marrrk/LoRaDongle/docs/assets/images/LoRaDongle_V1.jpg

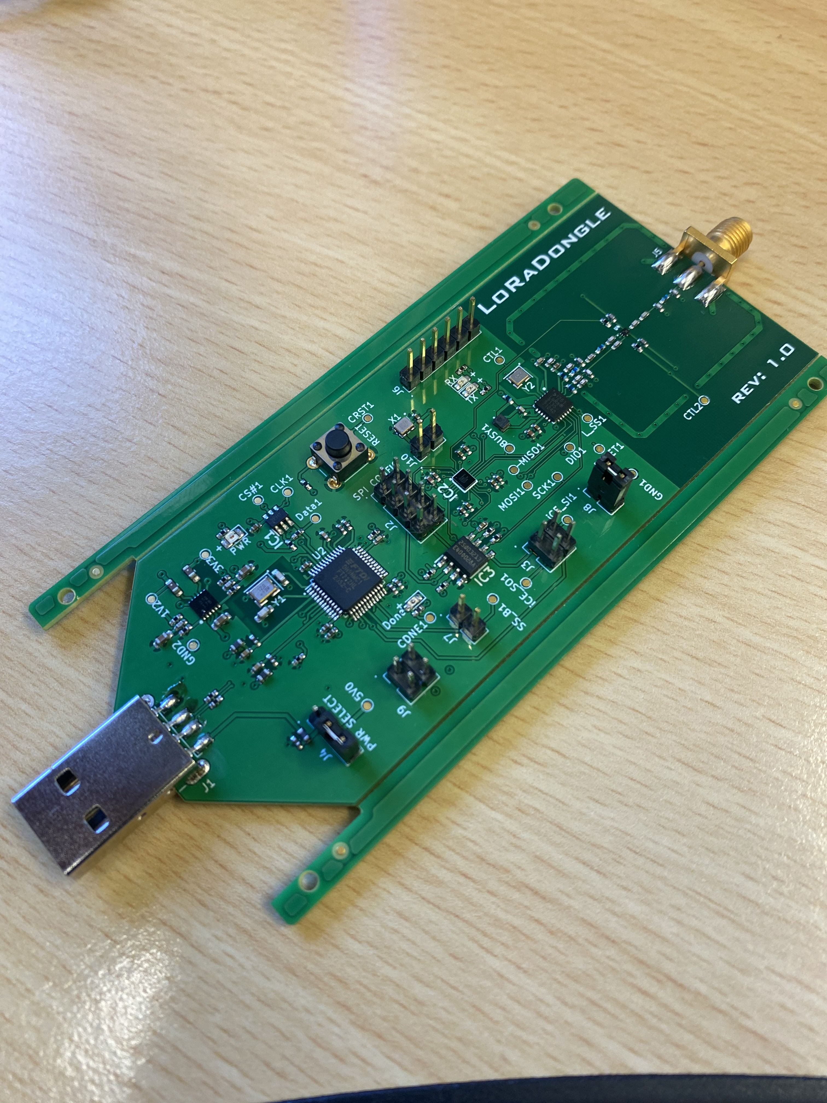
docs/assets/images/LoRaDongle_V1.jpg
