marrrk/LoRaDongle/testing/latency_tests/Test_11.csv

Success | Time to Send | Time to Receive | Message Size | RSSI | RSSI Despread | SNR | Timestamp
False | 9251.708523809524 |  |  |  |  |  | 17:50:10
False | 9251.708523809524 | 18680.361904761907 | 15 | -1.0 | -0.5 | 1.25 | 17:50:22
False | 9251.708523809524 |  |  |  |  |  | 17:50:58
False | 9251.708523809524 | 18680.49219047619 | 15 | -0.5 | -0.5 | 1.25 | 17:51:09
False | 9251.708523809524 |  |  |  |  |  | 17:51:46
False | 9251.708523809524 | 18680.49219047619 | 15 | -0.5 | -1.0 | 1.0 | 17:51:57
False | 9251.708523809524 |  |  |  |  |  | 17:52:34
False | 9251.708523809524 | 18680.49219047619 | 15 | -0.5 | -0.5 | 1.5 | 17:52:45
False | 9251.708523809524 | 18690.915047619048 | 15 | -0.5 | -0.5 | 1.25 | 17:53:09
False | 9251.708523809524 | 18691.17561904762 | 15 | -0.5 | -0.5 | 1.5 | 17:53:33
False | 9251.708523809524 | 18691.17561904762 | 15 | -0.5 | -0.5 | 1.25 | 17:53:57
False | 9251.708523809524 |  |  |  |  |  | 17:54:33
False | 9251.708523809524 |  |  |  |  |  | 17:54:57
False | 9251.708523809524 | 18677.886476190477 | 15 | -0.5 | -0.5 | 1.25 | 17:55:08
False | 9251.708523809524 |  |  |  |  |  | 17:55:45
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
