marrrk/LoRaDongle/testing/latency_tests/Test_12.csv

Success | Time to Send | Time to Receive | Message Size | RSSI | RSSI Despread | SNR | Timestamp
True | 10831.610047619048 | 21850.332333333336 | 15 | -1.0 | -1.0 | 1.5 | 19:06:17
True | 10831.610047619048 | 21850.332333333336 | 15 | -1.0 | -1.0 | 1.75 | 19:06:43
True | 10831.610047619048 | 21850.332333333336 | 15 | -1.0 | -1.5 | 1.75 | 19:07:09
True | 10831.610047619048 | 21850.332333333336 | 15 | -1.0 | -1.5 | 1.75 | 19:07:35
True | 10831.610047619048 | 21850.332333333336 | 15 | -1.0 | -1.0 | 1.5 | 19:08:01
True | 10831.610047619048 | 21850.332333333336 | 15 | -1.0 | -1.5 | 1.75 | 19:08:27
True | 10831.610047619048 | 21850.332333333336 | 15 | -1.0 | -1.0 | 1.25 | 19:08:53
True | 10831.610047619048 | 21850.332333333336 | 15 | -1.0 | -1.5 | 1.75 | 19:09:18
True | 10831.610047619048 | 21850.332333333336 | 15 | -1.0 | -1.0 | 1.25 | 19:09:44
True | 10831.610047619048 | 21850.46261904762 | 15 | -1.0 | -1.0 | 1.5 | 19:10:10
True | 10831.610047619048 | 21850.332333333336 | 15 | -1.0 | -1.0 | 1.75 | 19:10:36
True | 10831.610047619048 | 21850.332333333336 | 15 | -1.0 | -1.5 | 1.75 | 19:11:02
True | 10831.610047619048 | 21850.332333333336 | 15 | -1.0 | -1.0 | 1.75 | 19:11:28
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
