marrrk/LoRaDongle/testing/latency_tests/Test_13.csv

Success | Time to Send | Time to Receive | Message Size | RSSI | RSSI Despread | SNR | Timestamp
True | 714.7719523809524 | 1553.8544761904761 | 15 | -0.5 | -0.5 | 3.25 | 19:49:16
True | 714.7719523809524 | 1554.375619047619 | 15 | -0.5 | -0.5 | 3.25 | 19:49:21
True | 714.7719523809524 | 1555.1573333333333 | 15 | -0.5 | -0.5 | 3.25 | 19:49:26
True | 714.7719523809524 | 1543.952761904762 | 15 | -0.5 | -0.5 | 3.25 | 19:49:31
True | 714.7719523809524 | 1554.5059047619047 | 15 | -0.5 | -0.5 | 3.25 | 19:49:35
True | 714.7719523809524 | 1552.160761904762 | 15 | -0.5 | -0.5 | 3.25 | 19:49:40
True | 714.7719523809524 | 1553.8544761904761 | 15 | -0.5 | -0.5 | 3.25 | 19:49:45
True | 714.7719523809524 | 1554.375619047619 | 15 | -0.5 | -0.5 | 3.25 | 19:49:50
True | 714.7719523809524 | 1555.1573333333333 | 15 | -0.5 | -0.5 | 3.25 | 19:49:55
True | 714.7719523809524 | 1543.952761904762 | 15 | -0.5 | -0.5 | 3.25 | 19:50:00
True | 714.7719523809524 | 1554.5059047619047 | 15 | -0.5 | -0.5 | 3.25 | 19:50:05
True | 714.7719523809524 | 1552.160761904762 | 15 | -0.5 | -0.5 | 3.25 | 19:50:10
True | 714.7719523809524 | 1553.8544761904761 | 15 | -0.5 | -0.5 | 3.25 | 19:50:15
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
