marrrk/LoRaDongle/testing/latency_tests/Test_14.csv

Success | Time to Send | Time to Receive | Message Size | RSSI | RSSI Despread | SNR | Timestamp
True | 3617.112476190476 | 7372.199476190476 | 15 | -0.5 | -0.5 | 2.0 | 19:56:32
True | 3617.112476190476 | 7372.199476190476 | 15 | -0.5 | -0.5 | 2.0 | 19:56:43
True | 3617.112476190476 | 7372.199476190476 | 15 | -0.5 | -0.5 | 2.0 | 19:56:53
True | 3617.112476190476 | 7372.199476190476 | 15 | -0.5 | -0.5 | 2.0 | 19:57:04
True | 3617.112476190476 | 7372.199476190476 | 15 | -0.5 | -0.5 | 2.0 | 19:57:15
True | 3617.112476190476 | 7372.199476190476 | 15 | -0.5 | -0.5 | 2.0 | 19:57:26
True | 3617.112476190476 | 7372.199476190476 | 15 | -0.5 | -0.5 | 2.0 | 19:57:37
True | 3617.112476190476 | 7372.199476190476 | 15 | -0.5 | -0.5 | 2.0 | 19:57:48
True | 3617.112476190476 | 7372.199476190476 | 15 | -0.5 | -0.5 | 2.0 | 19:57:59
True | 3617.112476190476 | 7372.199476190476 | 15 | -0.5 | -0.5 | 2.0 | 19:58:10
True | 3617.112476190476 | 7372.06919047619 | 15 | -0.5 | -0.5 | 2.0 | 19:58:21
True | 3617.112476190476 | 7372.199476190476 | 15 | -0.5 | -0.5 | 2.0 | 19:58:32
True | 3617.112476190476 | 7372.199476190476 | 15 | -0.5 | -0.5 | 2.0 | 19:58:43
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
