marrrk/LoRaDongle/PCB/LoRaDongle_iCE40_USB/manufacturing/rev 1.0/assembly/LoRaDongle_iCE40-F_Courtyard.pdf

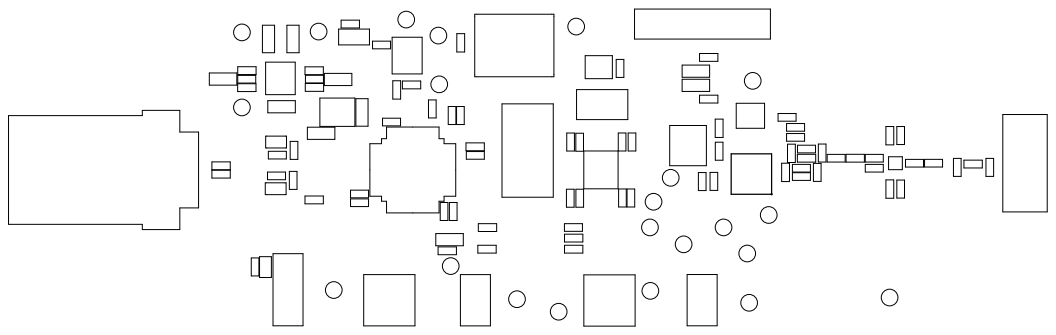
[picture p34: page 1]
