marrrk/LoRaDongle/PCB/LoRaDongle_iCE40_USB/manufacturing/rev 1.0/assembly/LoRaDongle_iCE40-User_Drawings.pdf

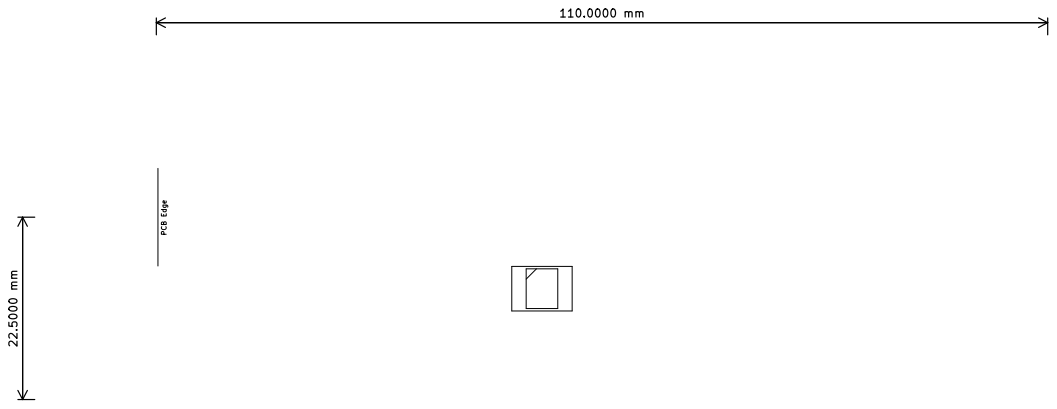
[picture p37: page 1]
