marrrk/LoRaDongle/firmware/pingpong_test/Radio/sx126x_hal.c

#include <generated/csr.h>
#include <stdint.h>
#include <stdbool.h>
#include <sx126x_hal.h>
#include <spi.h>
#include <stdio.h> // for printf functions
#include <time.h>

//// Constants
#define LORA_BUSY 1
#define LORA_DIO1 0
#define LORA_ANT_SW 0
#define LORA_RESET 1


/**
 *      Goal is to have spi_driver functions that will write bytes at a time. 
 *      These functions I think should break up the message byte by byte and use spi 
 *      class to send the message. SPI class takes in message and 
 */

sx126x_hal_status_t sx126x_hal_write( const void* context, const uint8_t* command, const uint16_t command_length, const uint8_t* data, const uint16_t data_length ) {
    sx126x_hal_status_t status; //update to remove the 1
    
    // Setting Command and Message Information
    //uint32_t ctrl = ((command_length + data_length) << 8) | (1 << 0);

    //SPI_control_write(ctrl); // set message length and start transmission

    SPI_control_length_write(8);
    SPI_cs_mode_write(1);    
    SPI_cs_sel_write(1);
    msleep(1);
    
    for (uint16_t i; i<command_length; i++) {
        SPI_mosi_write((uint32_t)*command++);
        SPI_control_start_write(0x1);;
        //printf("MISO: 0x%lx\n",SPI_miso_read()); // check if transmission has been successful

        msleep(1);
    }

    for (uint16_t i; i<data_length; i++){
        SPI_mosi_write((uint32_t)*data++);
        SPI_control_start_write(0x1);;
        //printf("MISO: 0x%lx\n",SPI_miso_read()); // check if transmission has been successful
        msleep(1);
    }

    SPI_cs_sel_write(0);

    status = (sx126x_hal_status_t) wait_tx_rx_done();

    return status;
}



sx126x_hal_status_t sx126x_hal_read( const void* context, const uint8_t* command, const uint16_t command_length, uint8_t* data, const uint16_t data_length ) {
    sx126x_hal_status_t status; //update to remove the 1

    
    SPI_control_length_write(8);
    SPI_cs_mode_write(1);    
    SPI_cs_sel_write(1);
    msleep(1);
    
    for (uint16_t i; i<command_length; i++) {
        SPI_mosi_write((uint32_t)*command++);
        SPI_control_start_write(0x1);;
        //printf("MISO: 0x%lx\n",SPI_miso_read()); // check if transmission has been successful
        msleep(1);
    }

    for (uint16_t i; i<data_length; i++){
        SPI_control_start_write(0x1);;
        msleep(1);
        *data++ = (uint8_t)SPI_miso_read();
        //printf("MISO: 0x%lx\n",SPI_miso_read()); // check if transmission has been successful

    }

    SPI_cs_sel_write(0);

    status = (sx126x_hal_status_t) wait_tx_rx_done();

    return status;
}


sx126x_hal_status_t sx126x_hal_reset( const void* context ){
    /*
    From the nucleo code: sx126x-hal.cpp
        disable_irq - looks like an stm specific thing
        wait 20 ms
        set the Reset pin to 0
        wait 50 ms
        set the Reset pin to 1
        wait 20 ms
        enable_irq
    */

    lora_config_out_write( lora_config_out_read() & ~(1 << LORA_RESET) );  // set reset pin to 0
    msleep(50);
    lora_config_out_write(lora_config_out_read() | (1 << LORA_RESET) );     // set reset pin to 1
    msleep(20);

    return (sx126x_hal_status_t)0;
}

sx126x_hal_status_t sx126x_hal_wakeup( const void* context ){
    /*
    from nucleo code:
        disbale irq
        get status from the radio (write a get status command to the radio/read MISO line ?)

        wait for radio to not be busy
        enable irq

        turn on AntSw

        *** looks to be more complex i think ***
    */
    while(lora_busy_in_read() == 0x1);
    //lora_config_out_write(lora_config_out_read() | (1 << LORA_ANT_SW) );



    return (sx126x_hal_status_t)0;
}
