marrrk/LoRaDongle/firmware/pingpong_test/peripherals/dio1.h

#ifndef __DIO_H
#define __DIO_H

#ifdef __cplusplus
extern "C" {
#endif

//function definitions and variables
void dio1_init(void);
void dio1_isr(void);

#ifdef __cplusplus
}
#endif


#endif //__DIO_H
